pmrancuret/FanControl/Code/inc/fanControl.h

// Only modify this file to include
// - function definitions (prototypes)
// - include files
// - extern variable definitions
// In the appropriate section

#ifndef _FanControl_H_
#define _FanControl_H_

#define PRESCALE_FACTOR 1

/*******************************************************************************
 * GLOBALLY INCLUDED HEADER FILES
 ******************************************************************************/
#include "Arduino.h"
#include "fanControlUtils.h"
#include "LiquidCrystal.h"
#include "savedVars.h"
#include "fanCtrlStateMachine.h"

#endif /* _FanControl_H_ */
