pmrancuret/FanControl/Code/FanControl.cpp

// Do not remove the include below
#include "FanControl.h"


// The setup function is called once at startup of the sketch
void setup ( )
{
// Add your initialization code here
}

// The loop function is called in an endless loop
void loop ( )
{
// Add your repeated code here
}
